qppd/IoT-Bike-Tracker/Source/BikeTracker/ModeConfig.h

// ModeConfig.h
// Configuration for BikeTracker modes

#ifndef MODECONFIG_H
#define MODECONFIG_H

// Operating modes
#define MODE_TESTING 0
#define MODE_PRODUCTION 1

// Set the current mode here (0 = Testing, 1 = Production)
#define CURRENT_MODE MODE_TESTING

// Configuration based on mode
#if CURRENT_MODE == MODE_TESTING
    #define DEBUG_ENABLED true
    #define GPS_UPDATE_INTERVAL 5000      // 5 seconds for testing
    #define SMS_ALERT_INTERVAL 30000      // 30 seconds for testing
    #define MOTION_THRESHOLD 5            // Lower threshold for testing
    #define MAX_SPEED_THRESHOLD 10        // km/h for testing alerts
    #define SLEEP_TIMEOUT 300000          // 5 minutes for testing
    #define DEEP_SLEEP_TIMEOUT 900000     // 15 minutes for testing
    #define AT_COMMAND_TESTING true       // Enable AT command testing in testing mode
    #define AT_TEST_TIMEOUT 60000         // 60 second timeout for long AT tests
    #define GPS_TESTING true              // Enable GPS testing in testing mode
    #define GPS_TEST_TIMEOUT 120000       // 120 second timeout for GPS fix tests
    #define GPS_NMEA_DISPLAY true         // Enable raw NMEA display in testing
#else
    #define DEBUG_ENABLED false
    #define GPS_UPDATE_INTERVAL 60000     // 1 minute for production
    #define SMS_ALERT_INTERVAL 300000     // 5 minutes for production
    #define MOTION_THRESHOLD 15           // Higher threshold for production
    #define MAX_SPEED_THRESHOLD 80        // km/h for production alerts
    #define SLEEP_TIMEOUT 1800000         // 30 minutes for production
    #define DEEP_SLEEP_TIMEOUT 7200000    // 2 hours for production
    #define AT_COMMAND_TESTING false      // Disable AT testing in production
    #define AT_TEST_TIMEOUT 10000         // 10 second timeout for production
    #define GPS_TESTING false             // Disable GPS testing in production
    #define GPS_TEST_TIMEOUT 30000        // 30 second timeout for production
    #define GPS_NMEA_DISPLAY false        // Disable raw NMEA in production
#endif

// Emergency contact (modify for production use)
#if CURRENT_MODE == MODE_TESTING
    #define EMERGENCY_CONTACT "+639634905586"  // Test number
#else
    #define EMERGENCY_CONTACT "+639634905586"  // Real emergency contact
#endif

// Debug macro
#if DEBUG_ENABLED
    #define DEBUG_PRINT(x) Serial.print(x)
    #define DEBUG_PRINTLN(x) Serial.println(x)
#else
    #define DEBUG_PRINT(x)
    #define DEBUG_PRINTLN(x)
#endif

#endif // MODECONFIG_H
