qppd/IoT-Bike-Tracker/Source/BikeTracker/Neo6mGPS.h

// Neo6mGPS.h
// Header for Neo6m GPS module

#ifndef NEO6MGPS_H
#define NEO6MGPS_H

#include <Arduino.h>
#include <SoftwareSerial.h>

struct GPSData {
    bool isValid;
    float latitude;
    float longitude;
    float altitude;
    float speed;
    int satellites;
    String timestamp;
    float hdop;
};

class Neo6mGPS {
public:
    Neo6mGPS(SoftwareSerial &serial);
    void begin(long baudrate = 9600);
    bool available();
    String read();
    GPSData parseGPSData();
    bool isLocationValid();
    String getLocationString();
    float getSpeed();
    void enableGGA();
    void enableRMC();
    
    // GPS Testing Functions
    void runBasicGPSTests();
    void runNMEATests();
    void runLocationTests();
    void runPerformanceTests();
    void runAllGPSTests();
    void printGPSTestResult(const String &testName, bool result, const String &details = "");
    bool testGPSResponse(int timeoutSeconds = 30);
    void printGPSTestHeader(const String &category);
    void displayRawNMEA(int duration = 10);
    void testSatelliteTracking(int duration = 30);
    void testGPSAccuracy();
    void printGPSStatus();
    
private:
    SoftwareSerial &gpsSerial;
    GPSData currentData;
    bool parseGGA(String sentence);
    bool parseRMC(String sentence);
    float convertDMSToDecimal(String dms, String direction);
    String rawData;
};

#endif // NEO6MGPS_H
